DrMikeG/Pedals/readme_img/51psoDps8AL._AC_.jpg

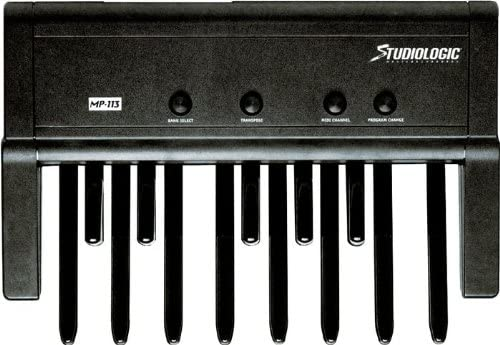
readme_img/51psoDps8AL._AC_.jpg
