DrMikeG/Pedals/readme_img/8959502_800.jpg

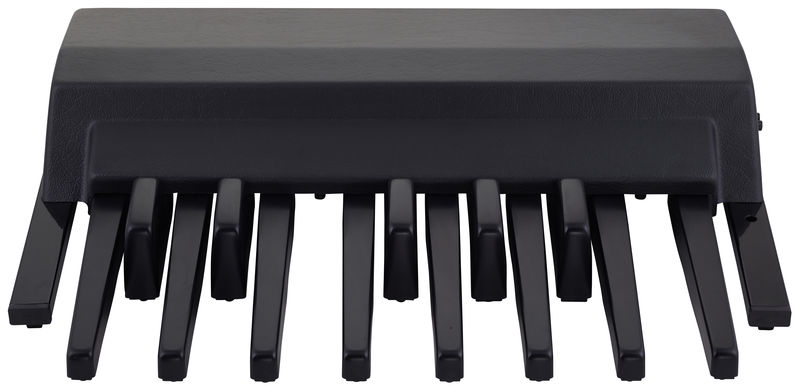
readme_img/8959502_800.jpg
