DrMikeG/Pedals/readme_img/10661656.jpg

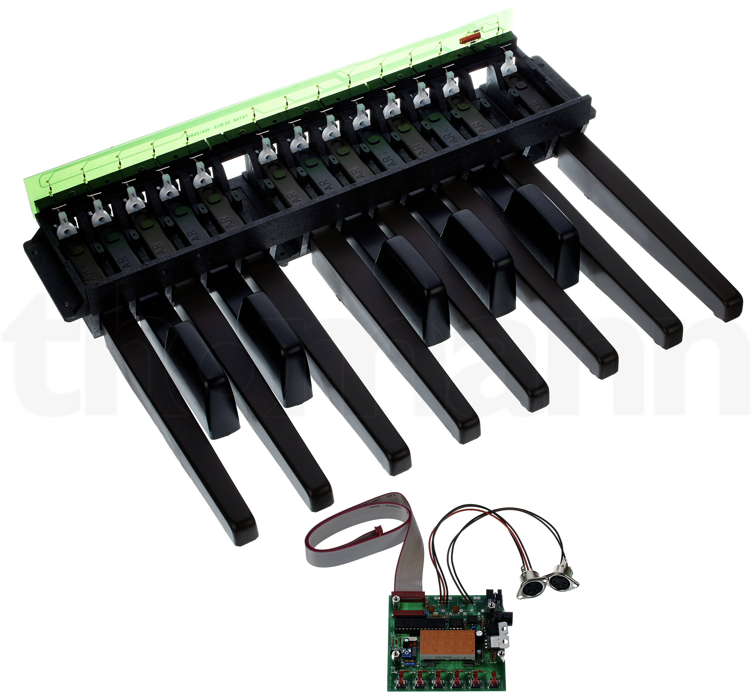
readme_img/10661656.jpg
