DrMikeG/Pedals/readme_img/10661661.jpg

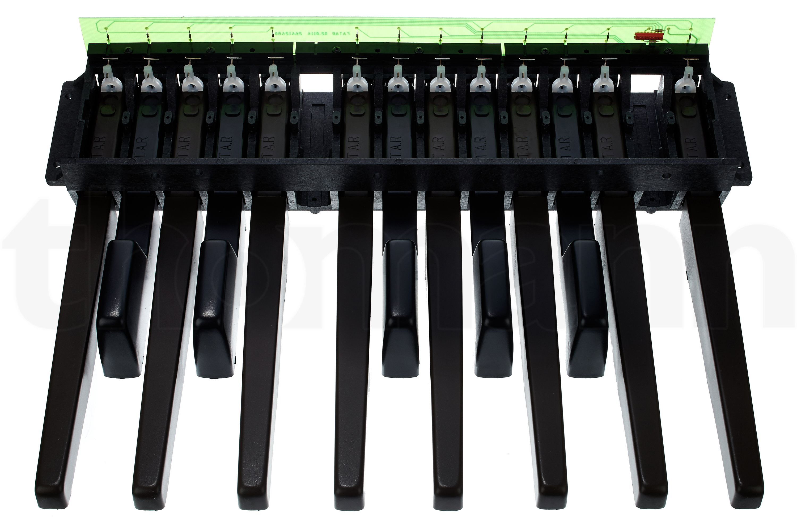
readme_img/10661661.jpg
