DrMikeG/Pedals/readme_img/10661666.jpg

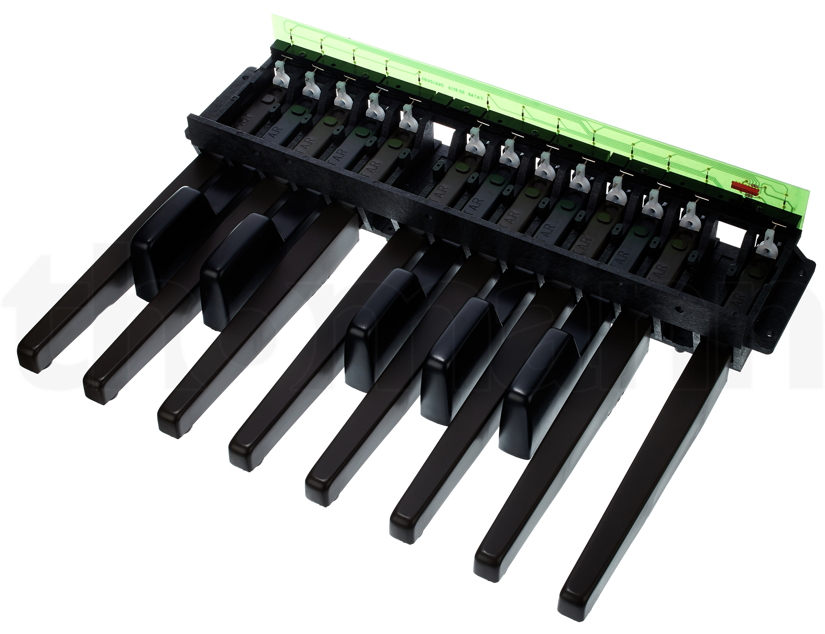
readme_img/10661666.jpg
