DrMikeG/Pedals/readme_img/10661676.jpg

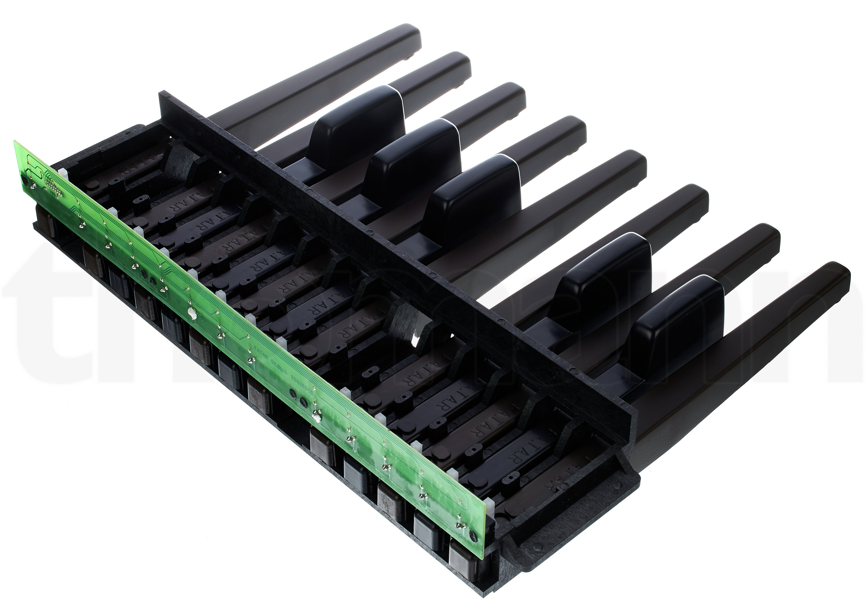
readme_img/10661676.jpg
