DrMikeG/Pedals/readme_img/20200915_185021.jpg

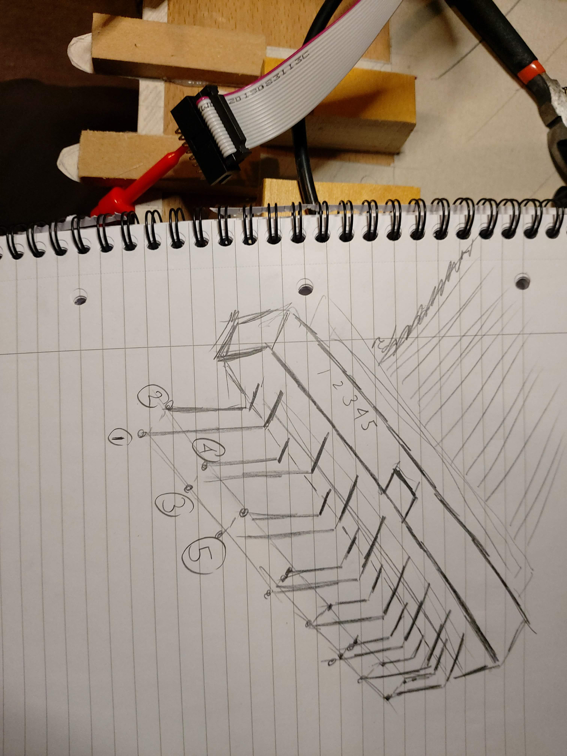
readme_img/20200915_185021.jpg
