DrMikeG/Pedals/readme_img/20200916_083039.jpg

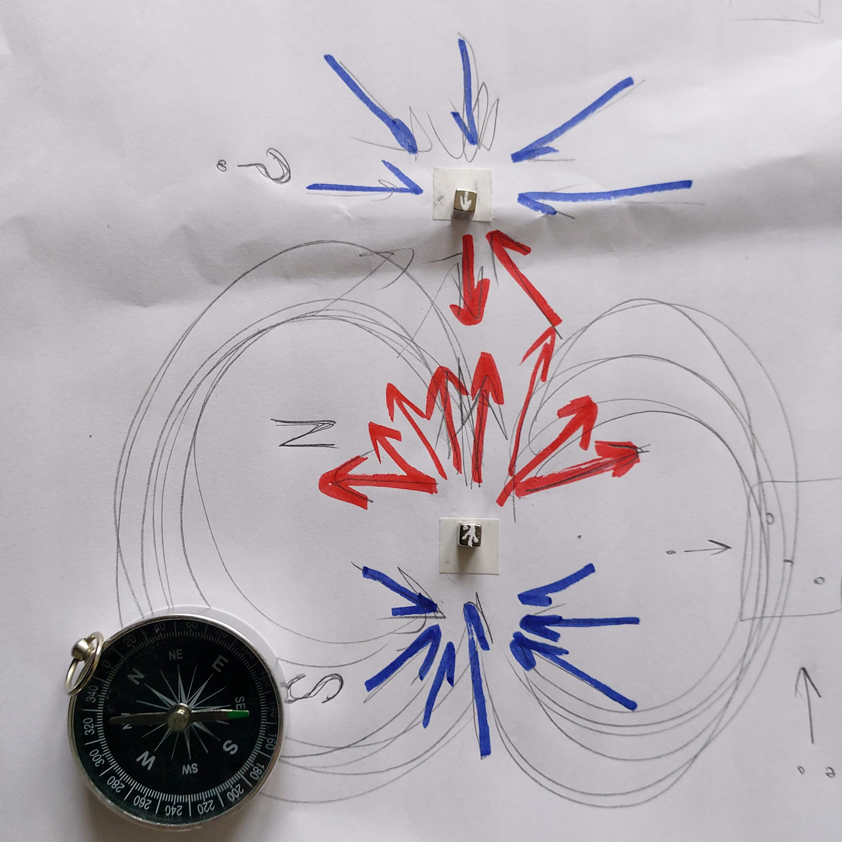
readme_img/20200916_083039.jpg
