DrMikeG/Pedals/readme_img/Hammond XPK130G-1-1200x1200.jpg

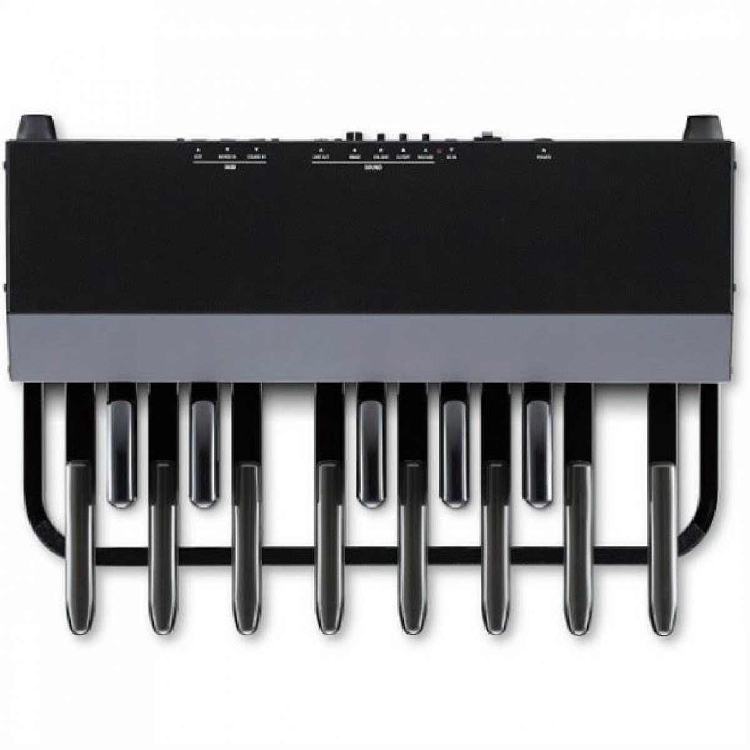
readme_img/Hammond XPK130G-1-1200x1200.jpg
