DrMikeG/Pedals/readme_img/hammond_xpk130g_pedalboard_2-1200x1200.jpg

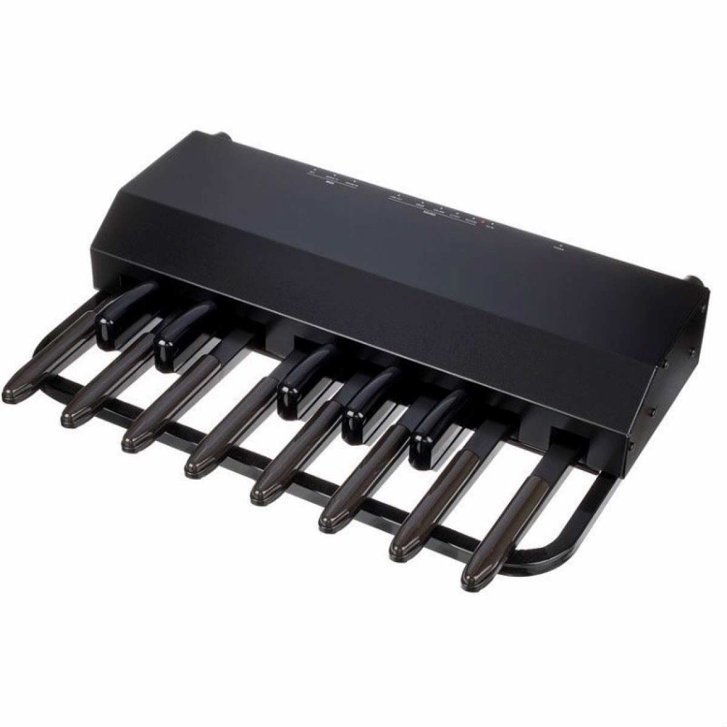
readme_img/hammond_xpk130g_pedalboard_2-1200x1200.jpg
