DrMikeG/Pedals/readme_img/notes.png

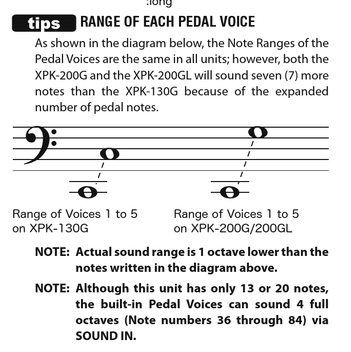
readme_img/notes.png
