DrMikeG/Pedals/readme_img/stud_01.jpg

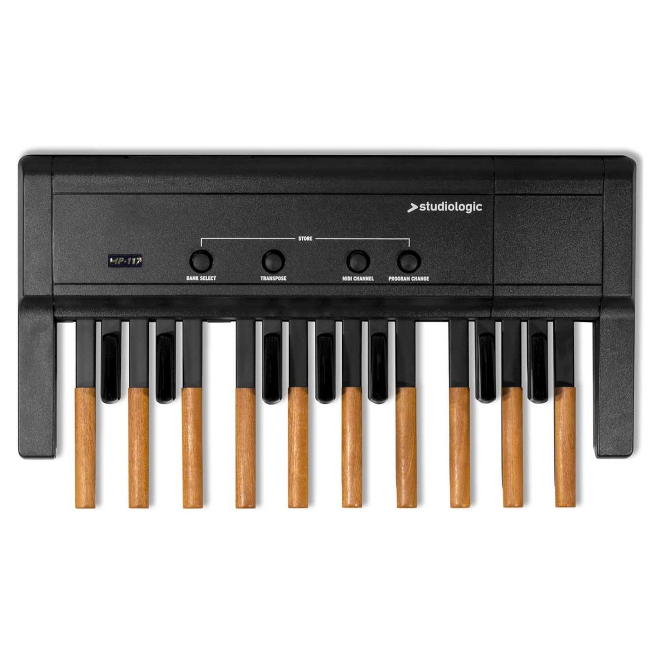
readme_img/stud_01.jpg
