DrMikeG/Pedals/readme_img/stud_02.jpg

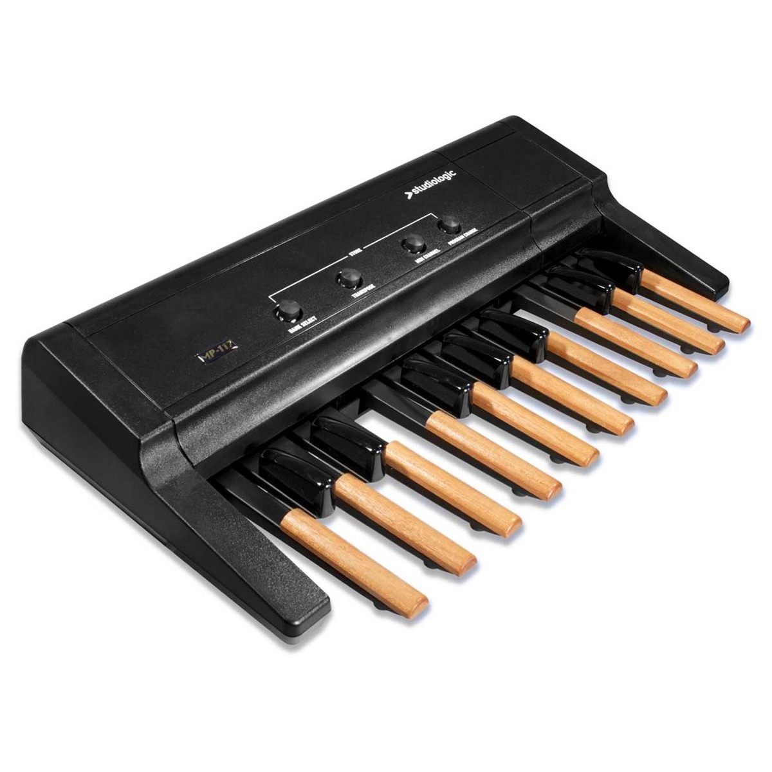
readme_img/stud_02.jpg
