DrMikeG/Pedals/teensie4/20200910_083512.jpg

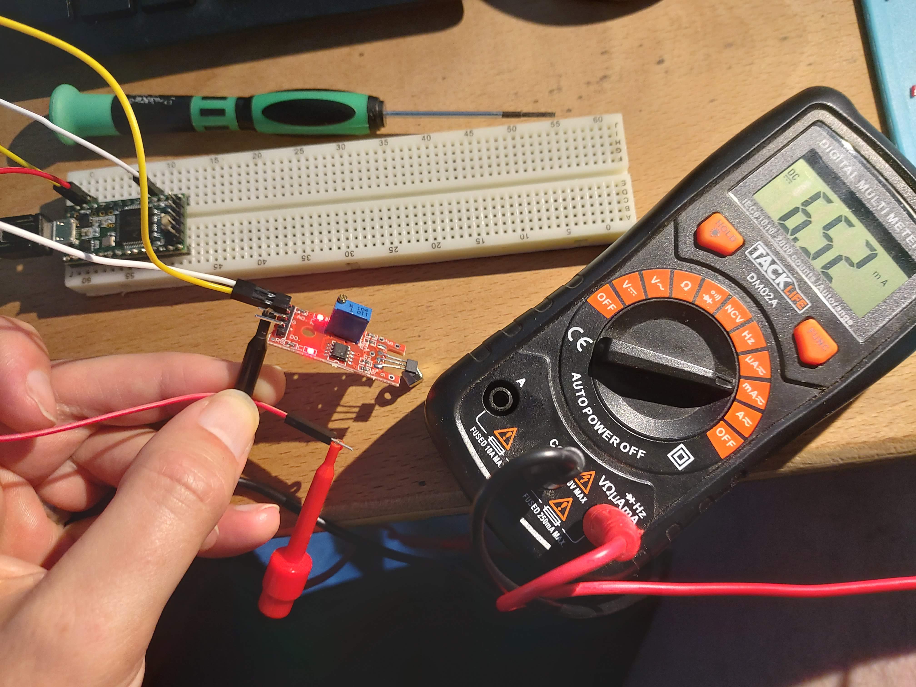
teensie4/20200910_083512.jpg
