DrMikeG/Pedals/teensie4/FC16P.png

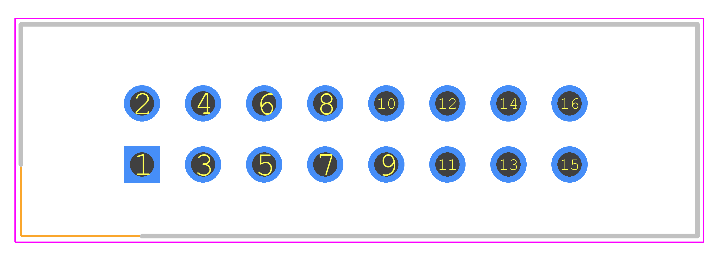
teensie4/FC16P.png
