DrMikeG/Pedals/prototype/KeyMechRig08.stl

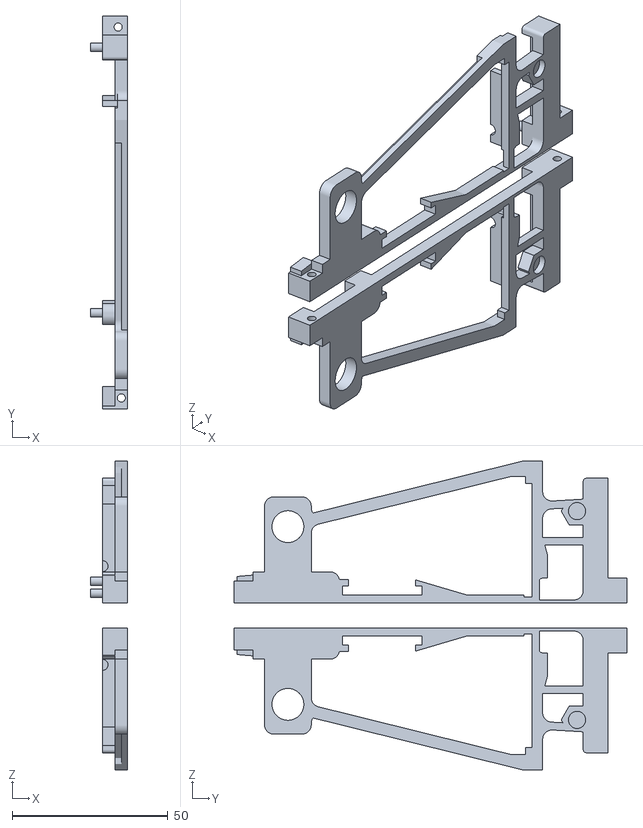
[picture p40: CAD file, 2020-10-22]
prototype/KeyMechRig08.stl
11.9 x 125.9 x 99.1
