DrMikeG/Pedals/prototype/Part1.stl

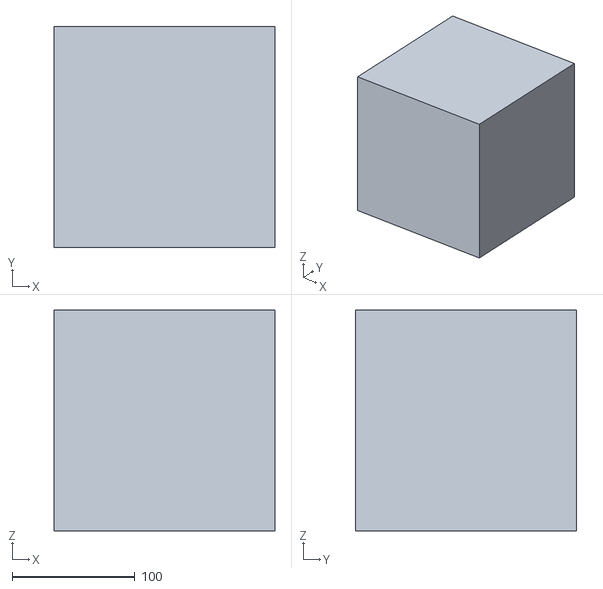
[picture p41: CAD file, 2020-10-22]
prototype/Part1.stl
180.0 x 180.0 x 180.0
