DrMikeG/Pedals/prototype/KeyMech05RearArm.stl

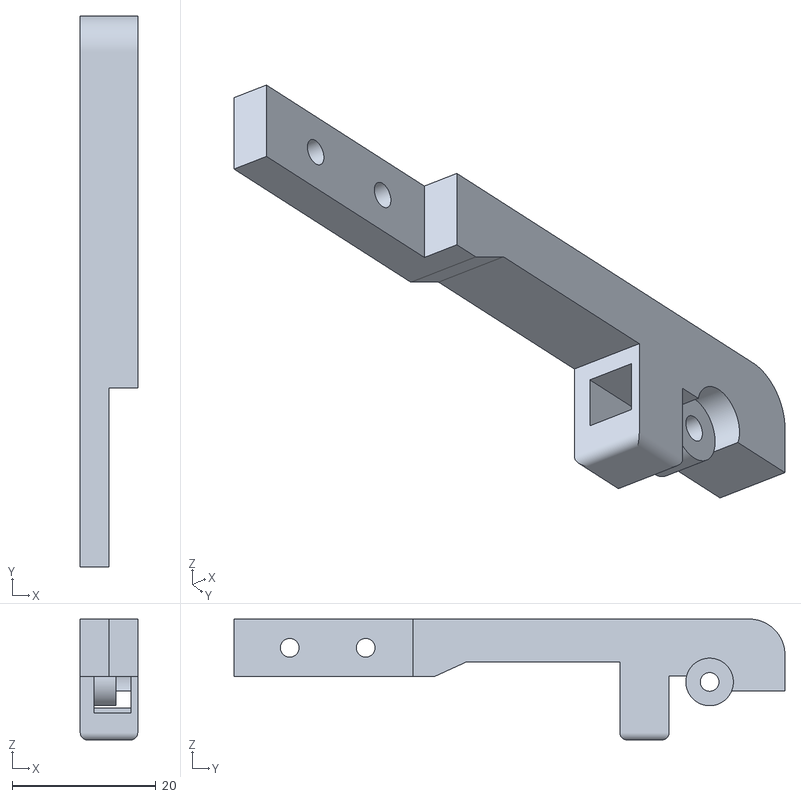
[picture p42: CAD file, 2020-10-22]
prototype/KeyMech05RearArm.stl
8.00 x 76.6 x 16.8
