DrMikeG/Pedals/prototype/BottomPlate02Right.stl

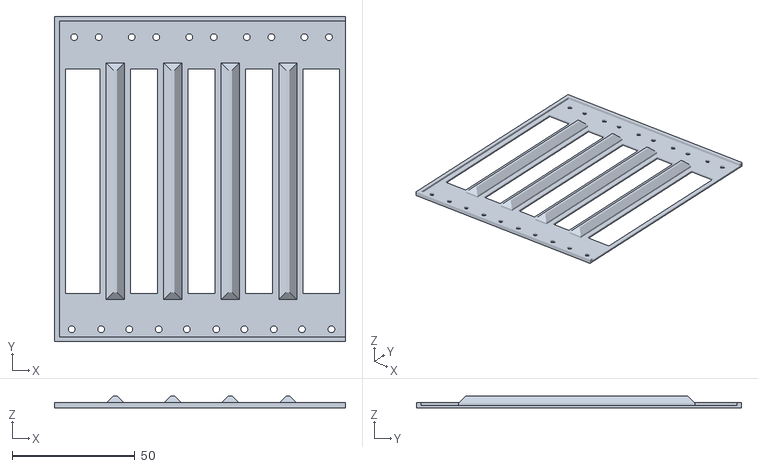
[picture p43: CAD file, 2020-10-22]
prototype/BottomPlate02Right.stl
118.5 x 132.5 x 5.00
