DrMikeG/Pedals/prototype/SingleSpacer1.stl

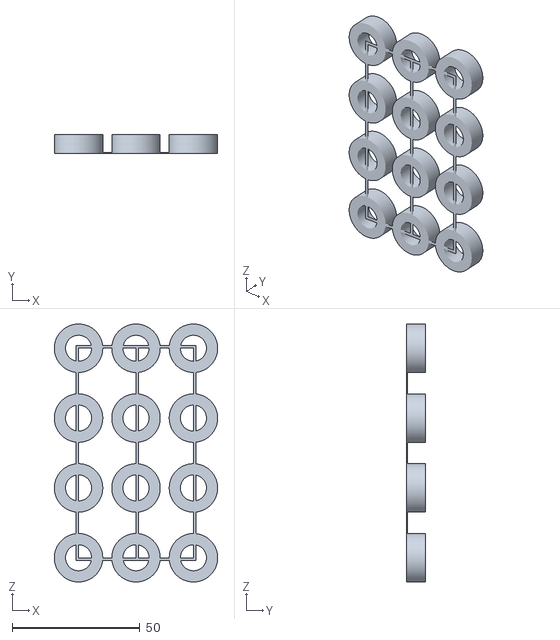
[picture p44: CAD file, 2020-10-22]
prototype/SingleSpacer1.stl
64.0 x 7.40 x 101.1
