DrMikeG/Pedals/prototype/BottomPlate01.stl

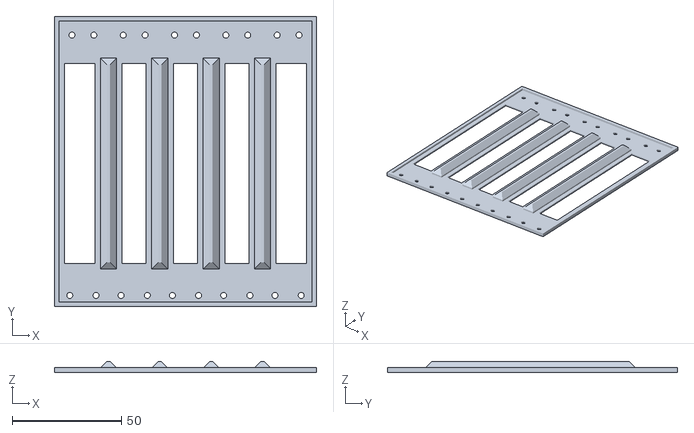
[picture p45: CAD file, 2020-10-22]
prototype/BottomPlate01.stl
119.8 x 132.5 x 5.00
