DrMikeG/Pedals/prototype/TeensieHolder.stl

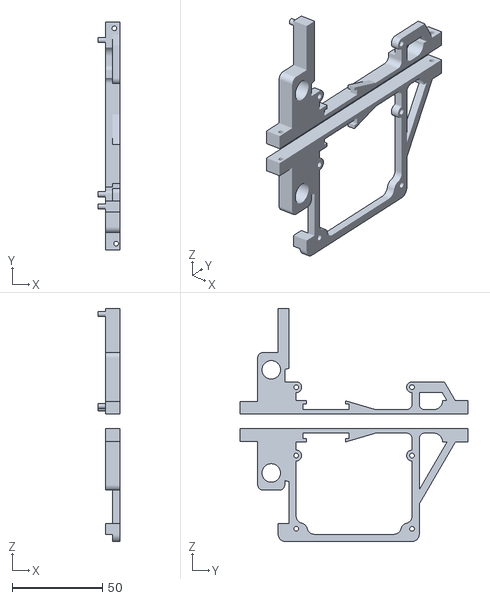
[picture p46: CAD file, 2020-10-22]
prototype/TeensieHolder.stl
11.9 x 125.9 x 128.8
