DrMikeG/Pedals/prototype/HingeEndDesign02.stl

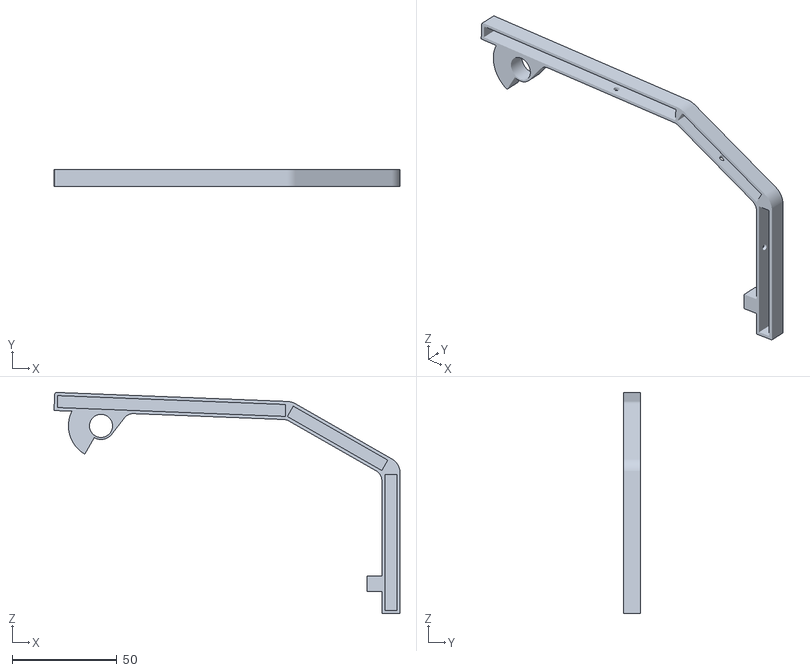
[picture p47: CAD file, 2020-10-22]
prototype/HingeEndDesign02.stl
165.3 x 8.00 x 105.6
