DrMikeG/Pedals/prototype/MidRailUnmeasured.stl

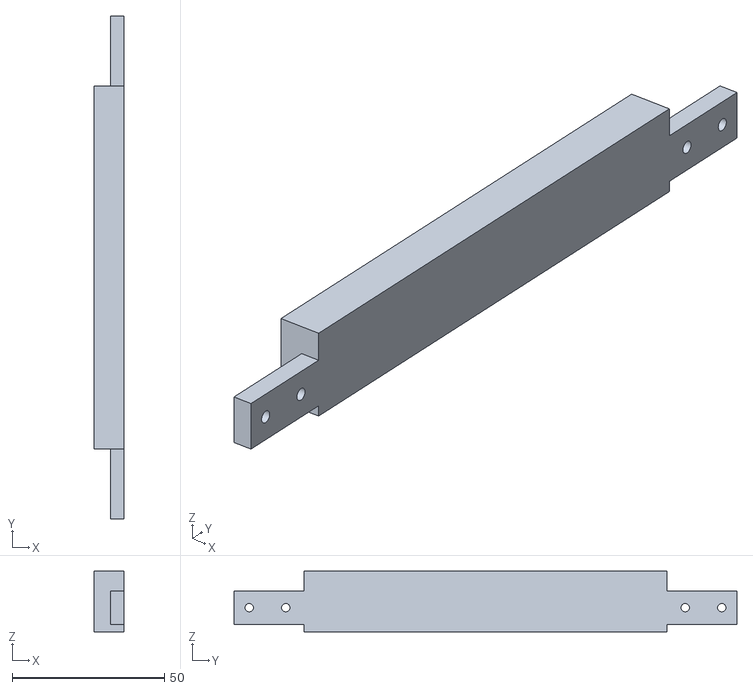
[picture p48: CAD file, 2020-10-22]
prototype/MidRailUnmeasured.stl
10.0 x 165.2 x 20.0
