DrMikeG/Pedals/prototype/DinSupportRearPlateRelief.stl

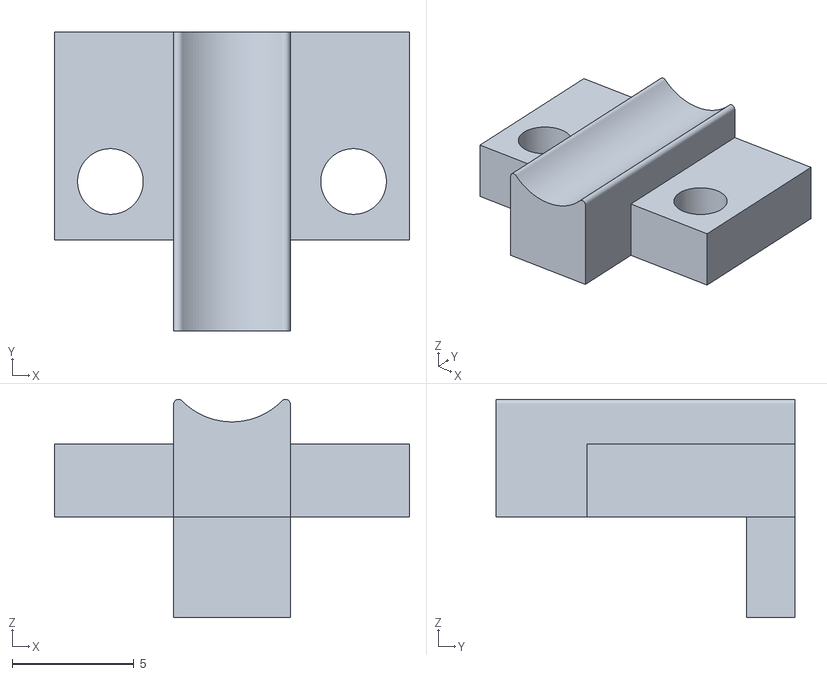
[picture p49: CAD file, 2020-10-22]
prototype/DinSupportRearPlateRelief.stl
14.6 x 12.3 x 8.98
