DrMikeG/Pedals/prototype/KeyMechRig07.stl

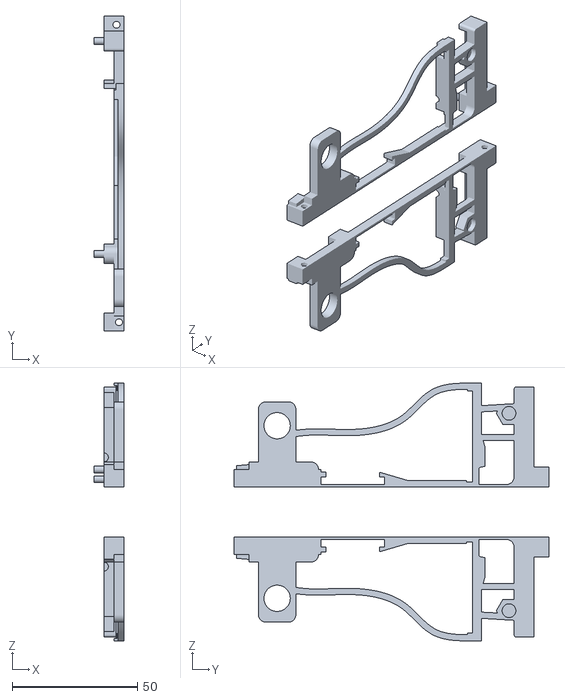
[picture p50: CAD file, 2020-09-17]
prototype/KeyMechRig07.stl
12.0 x 125.9 x 103.1
