DrMikeG/Pedals/prototype/KeyMech03RearArm.stl

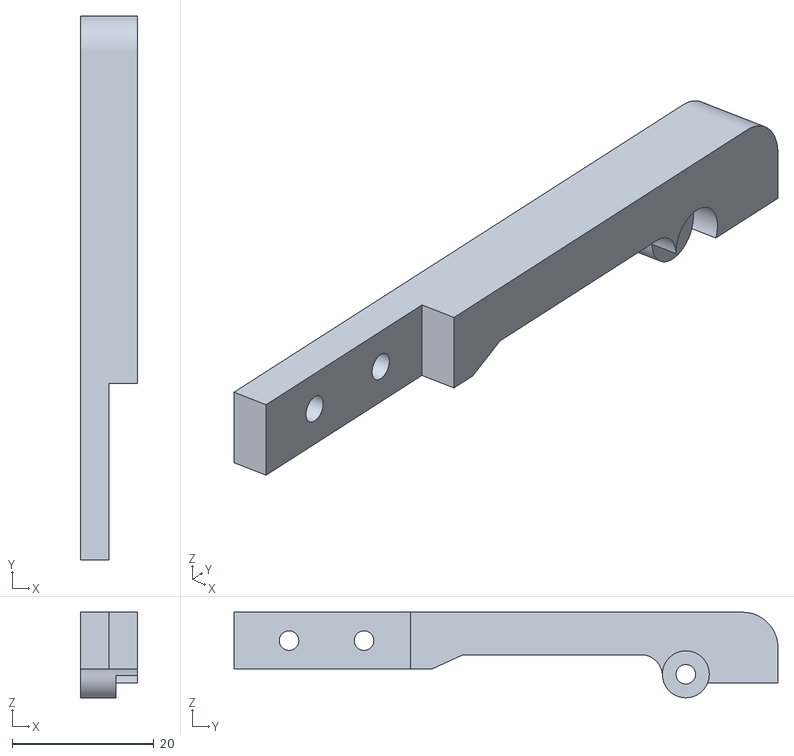
[picture p51: CAD file, 2020-09-15]
prototype/KeyMech03RearArm.stl
8.00 x 76.6 x 12.1
