DrMikeG/Pedals/prototype/KeyMechRig06.stl

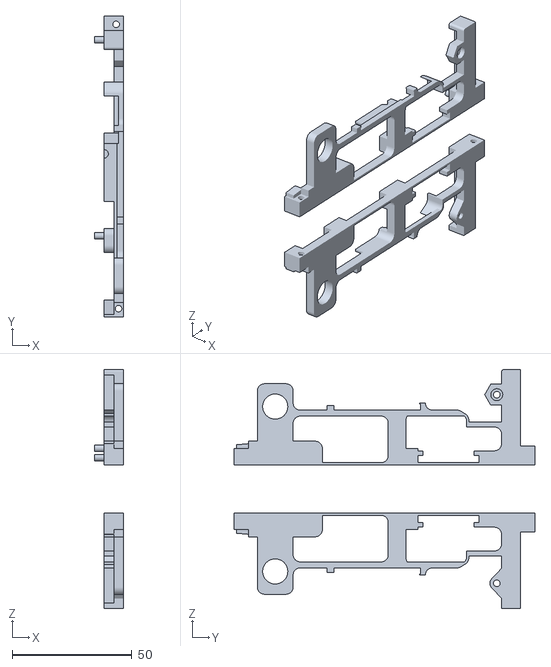
[picture p52: CAD file, 2020-09-15]
prototype/KeyMechRig06.stl
12.0 x 125.9 x 100.0
